Hashaamgtr/CAD_Project/review/06_CATIA_V5_2026_Final_Task/image18.png

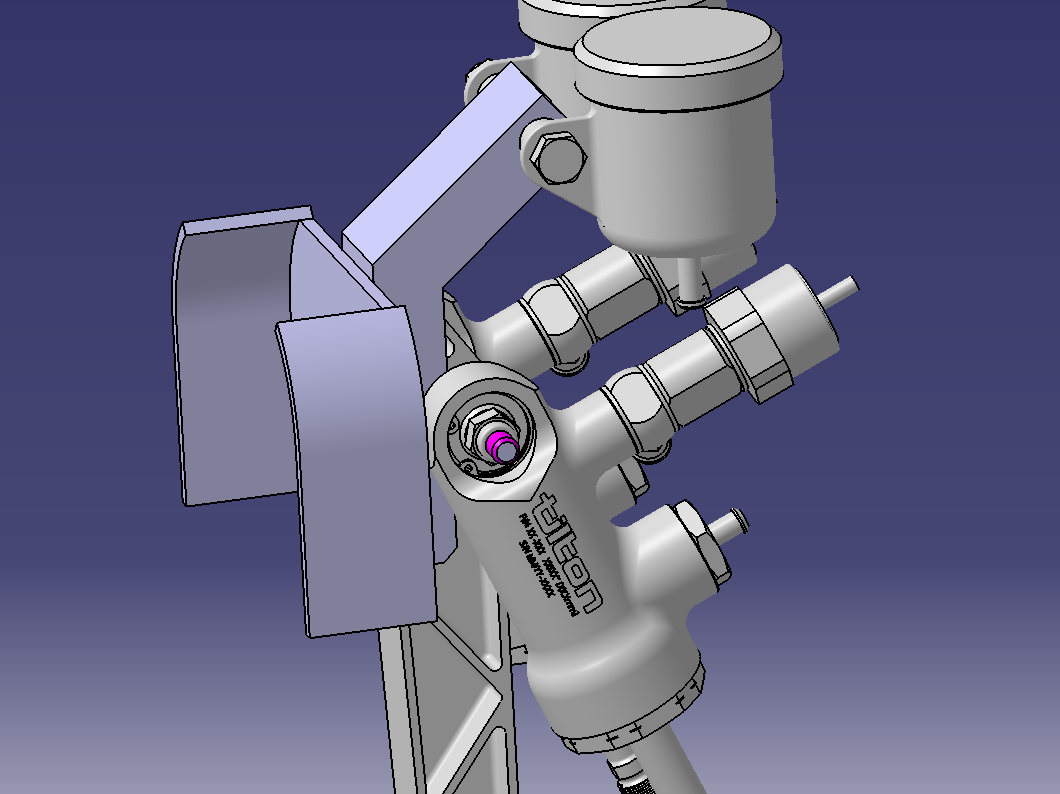
review/06_CATIA_V5_2026_Final_Task/image18.png
