Hashaamgtr/CAD_Project/review/06_CATIA_V5_2026_Final_Task/image20.png

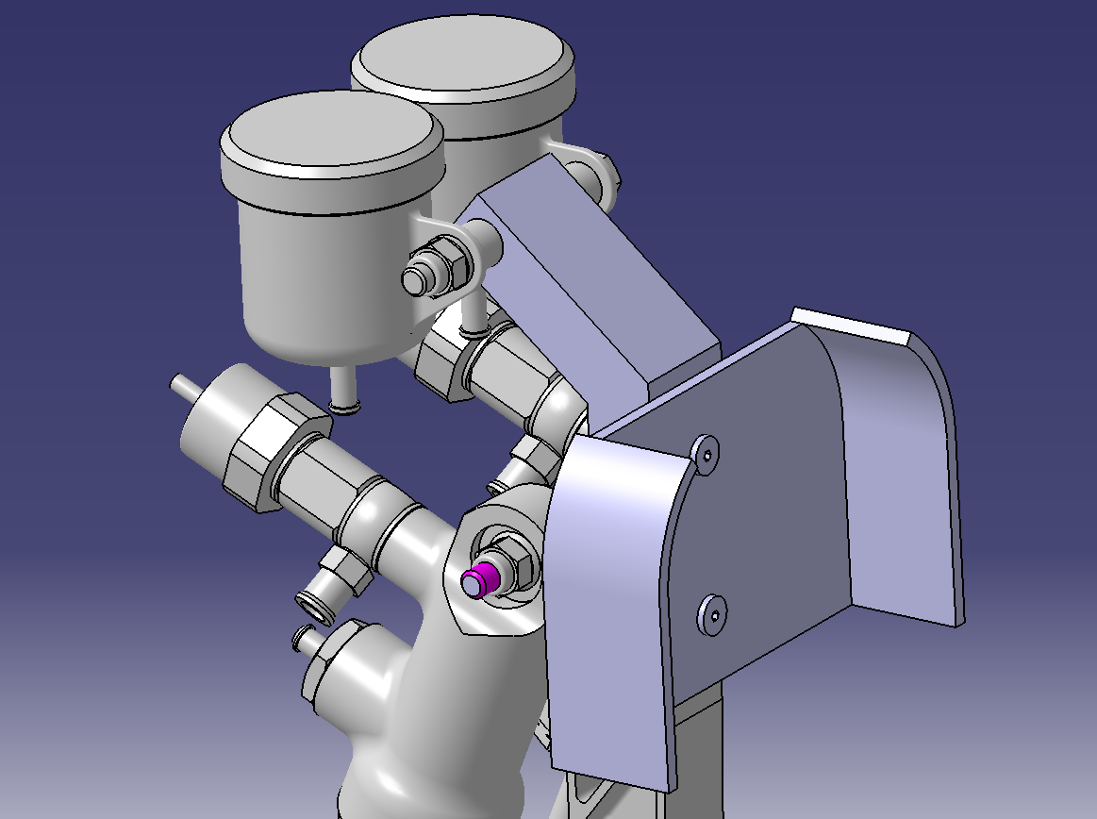
review/06_CATIA_V5_2026_Final_Task/image20.png
