Hashaamgtr/CAD_Project/review/Brake_Pedal_Shaft.bmp

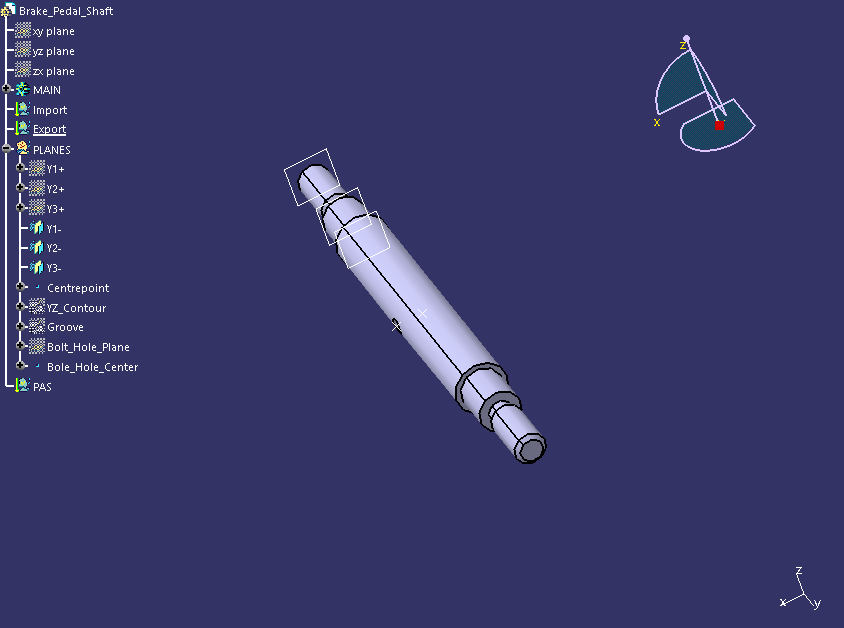
review/Brake_Pedal_Shaft.bmp
