Hashaamgtr/CAD_Project/review/Brake_Platform_2_positioned.bmp

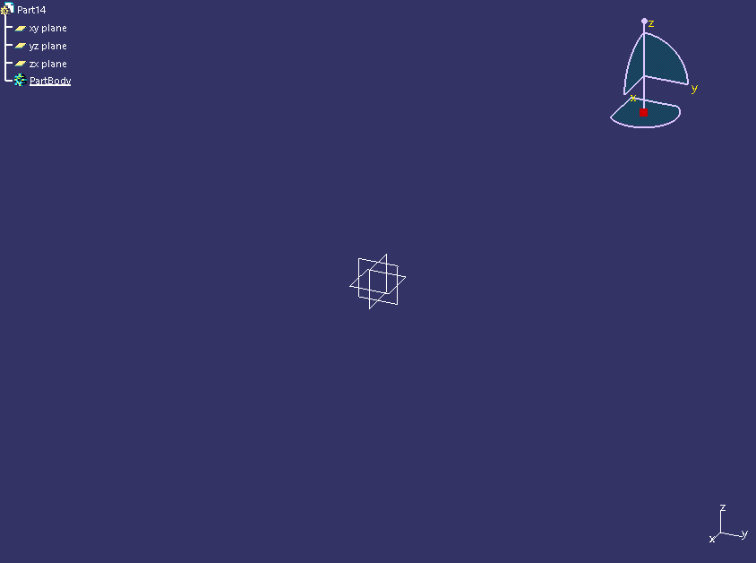
review/Brake_Platform_2_positioned.bmp
