Hashaamgtr/CAD_Project/review/BRK_PRS_Sensor_Connection_live.bmp

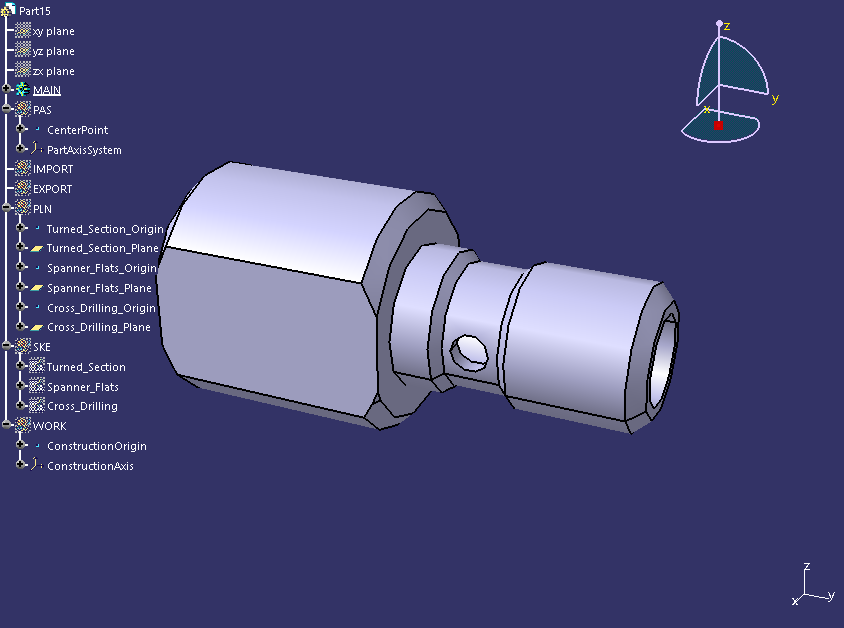
review/BRK_PRS_Sensor_Connection_live.bmp
