Hashaamgtr/CAD_Project/review/Foot_Plate.bmp

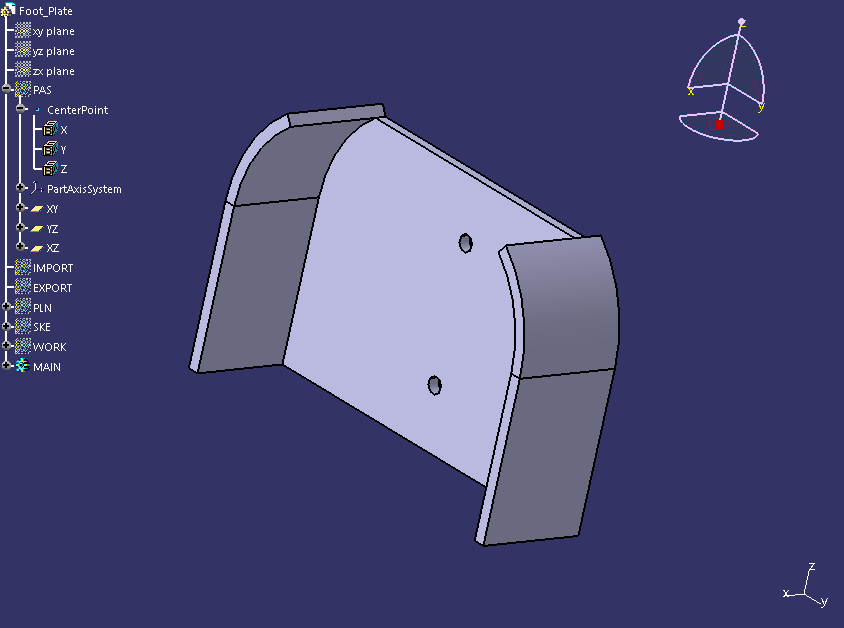
review/Foot_Plate.bmp
