Hashaamgtr/CAD_Project/review/MC_Inlet_live.bmp

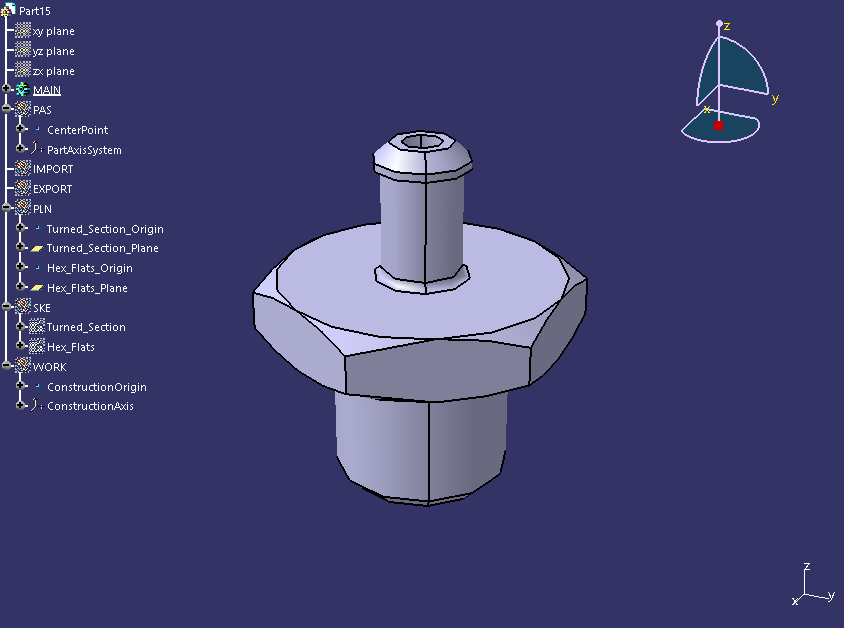
review/MC_Inlet_live.bmp
