Hashaamgtr/CAD_Project/review/Part1.bmp

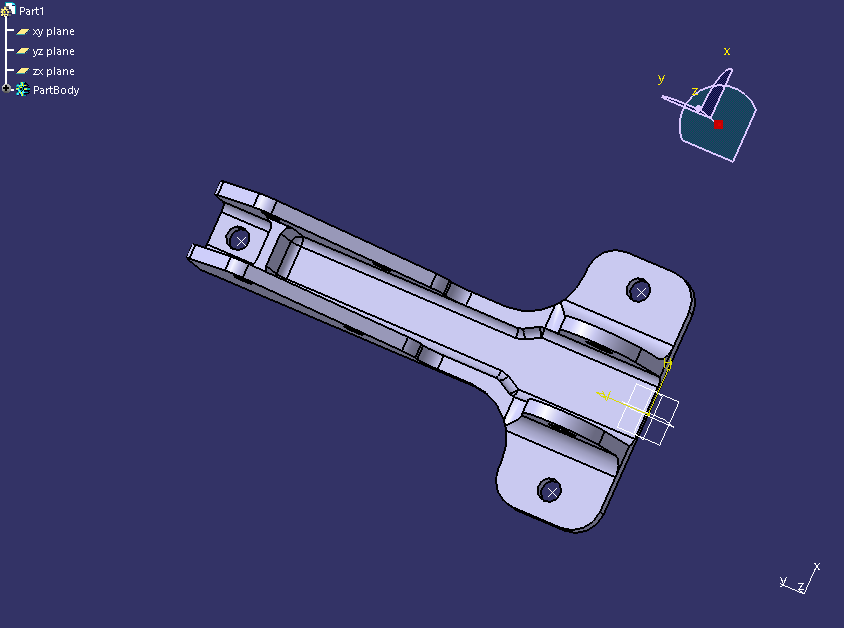
review/Part1.bmp
