Hashaamgtr/CAD_Project/review/Part 2&3.bmp

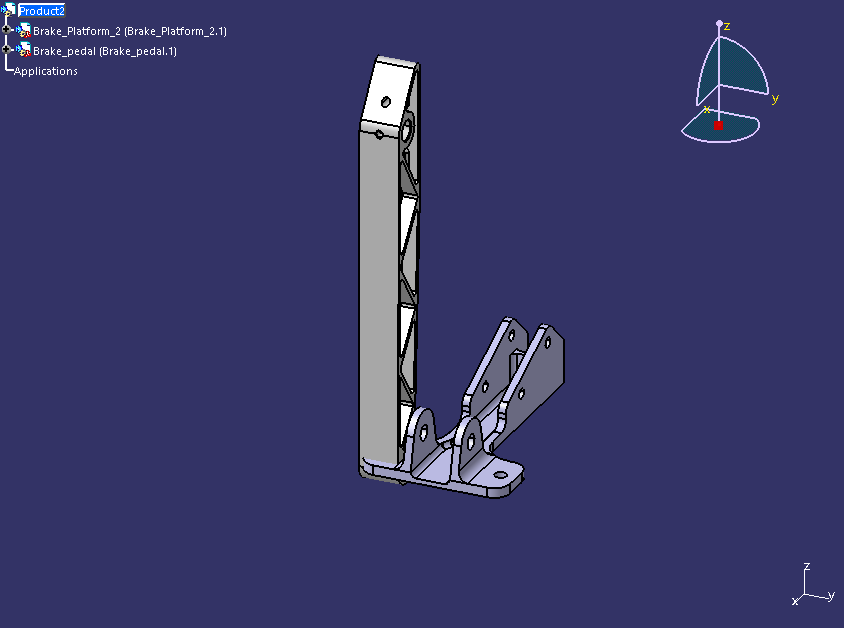
review/Part 2&3.bmp
