Hashaamgtr/CAD_Project/review/Part 2&3_actual.bmp

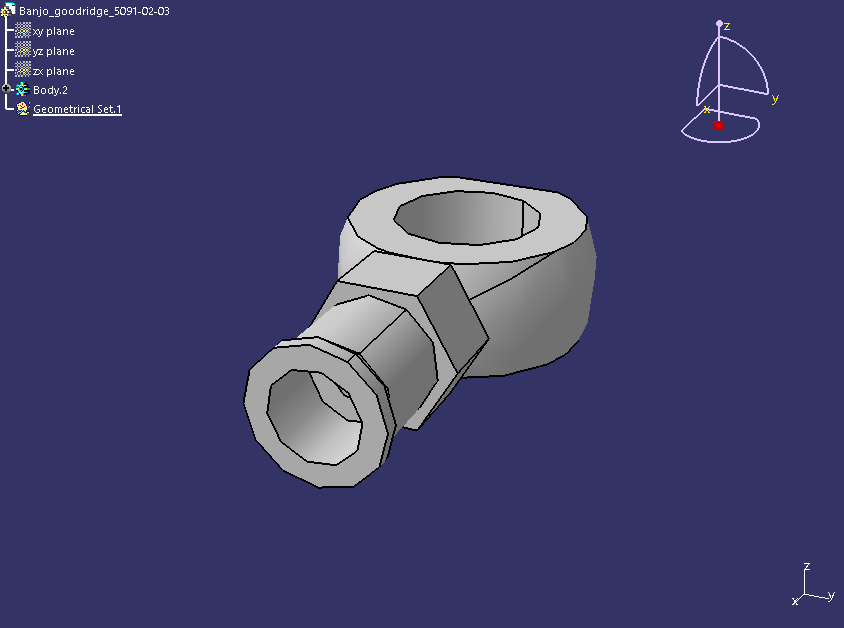
review/Part 2&3_actual.bmp
