Hashaamgtr/CAD_Project/review/Pedal_Body_live.bmp

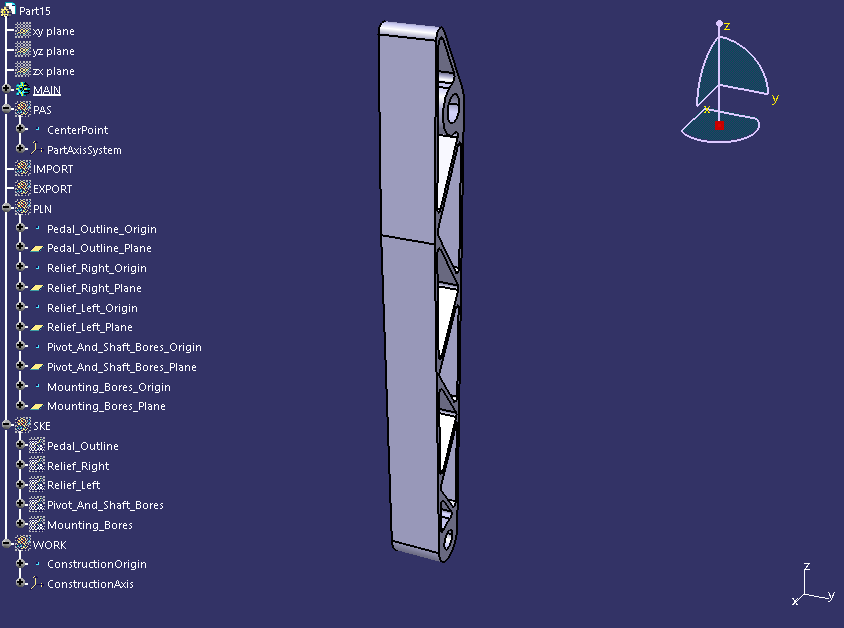
review/Pedal_Body_live.bmp
