Hashaamgtr/CAD_Project/review/Reservoir_Holder_positioned.bmp

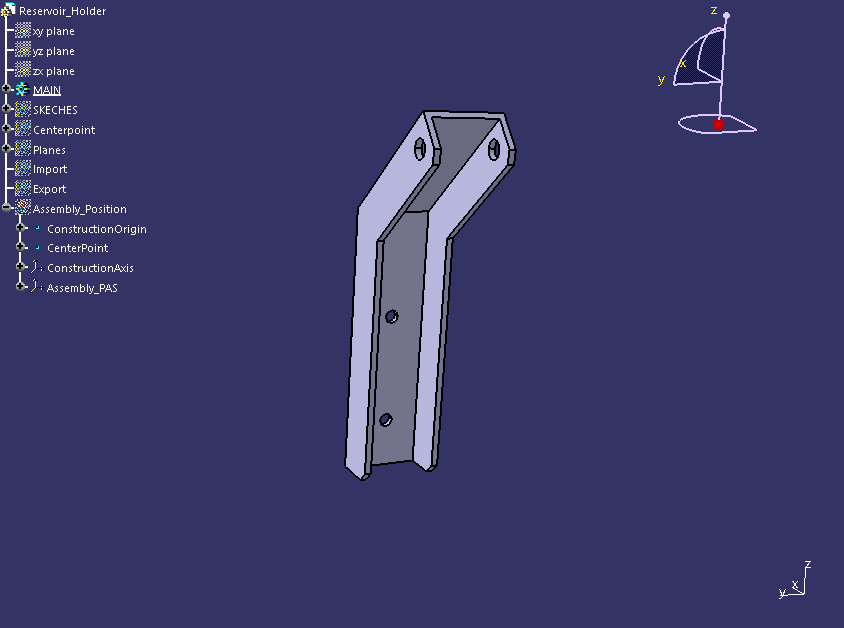
review/Reservoir_Holder_positioned.bmp
