Hashaamgtr/CAD_Project/reference_parts/Low_Head_M4x20.stp

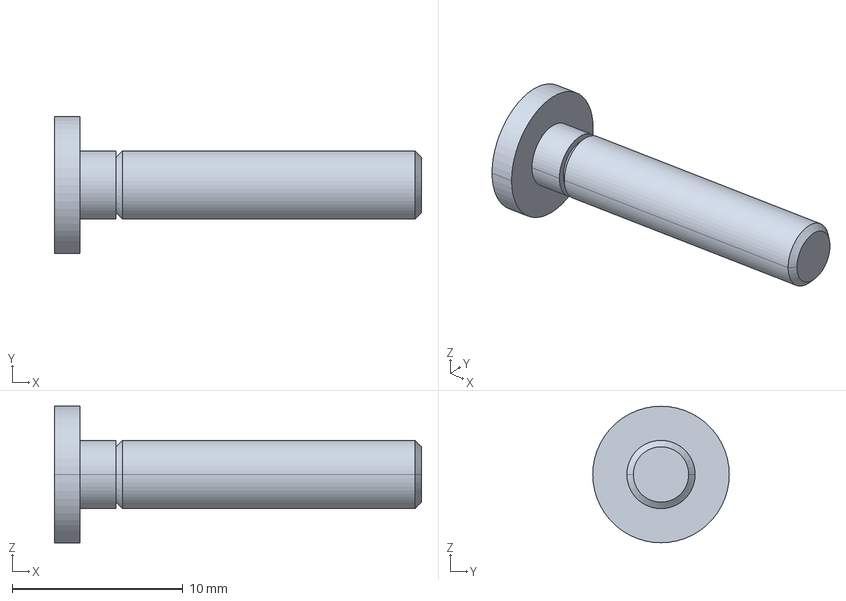
[picture p37: CAD file, 2026-10-06]
reference_parts/Low_Head_M4x20.stp
21.5 x 8.00 x 8.00 mm
