Hashaamgtr/CAD_Project/review/Brake_Platform_2_positioned.stp

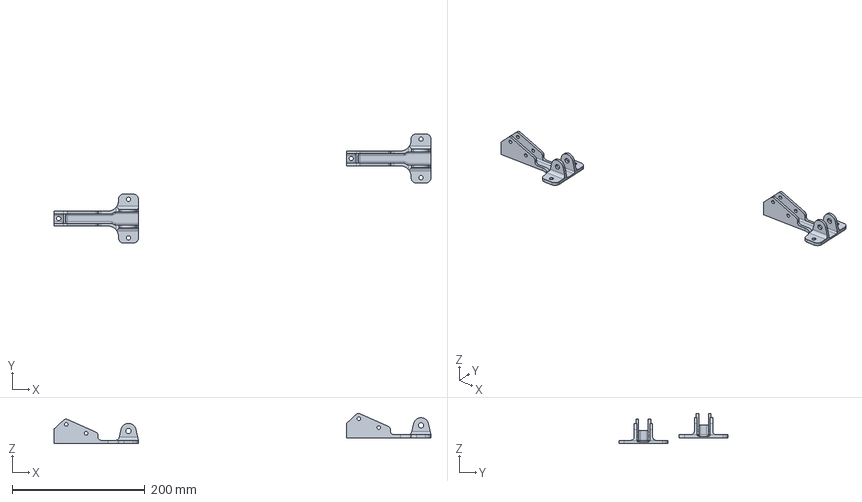
[picture p38: CAD file, 2026-10-06]
review/Brake_Platform_2_positioned.stp
567.0 x 164.5 x 45.4 mm
