Hashaamgtr/CAD_Project/reference_parts/Reservoir_Distance.stp

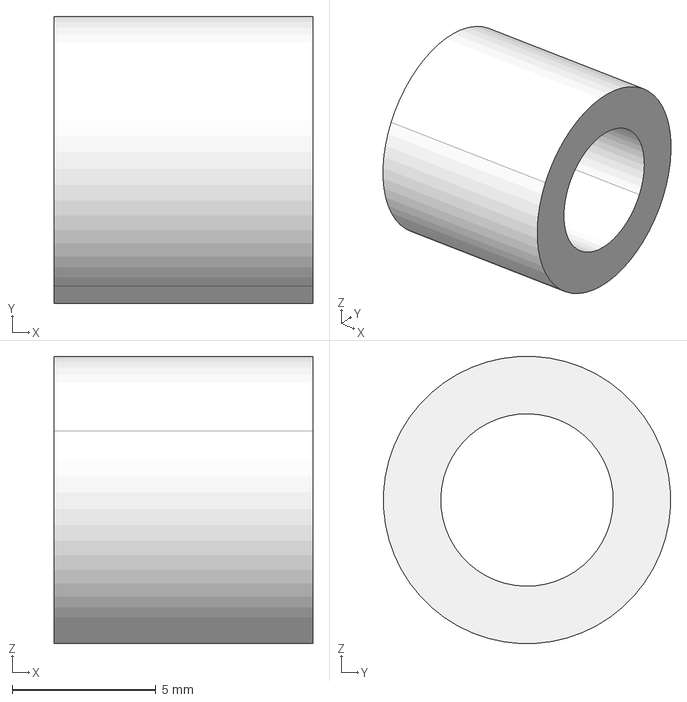
[picture p39: CAD file, 2026-10-06]
reference_parts/Reservoir_Distance.stp
9.00 x 9.99 x 9.99 mm
