Hashaamgtr/CAD_Project/reference_parts/BRK_PRS_Sensor.stp

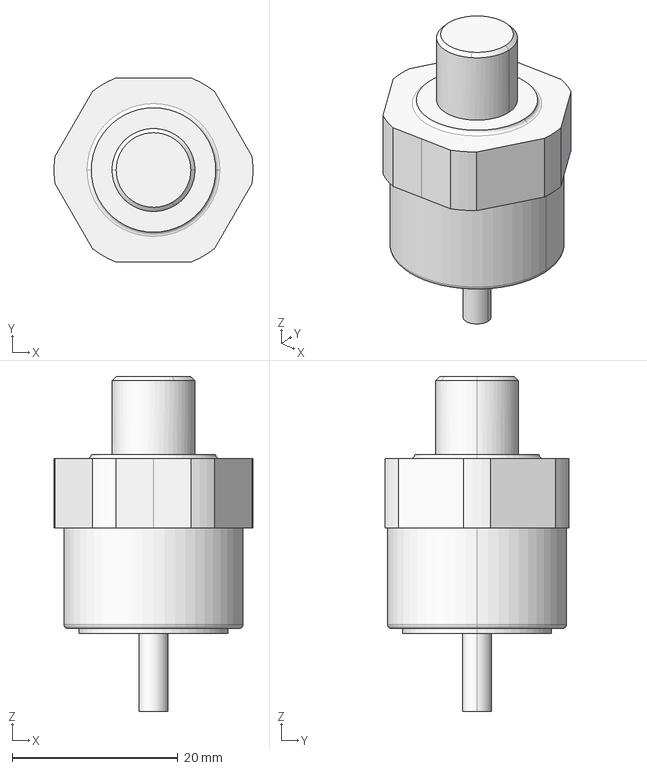
[picture p40: CAD file, 2026-10-06]
reference_parts/BRK_PRS_Sensor.stp
24.0 x 22.2 x 40.4 mm
