Hashaamgtr/CAD_Project/review/05_CATIA_V5_2026_ASSembly_Design/image16.png

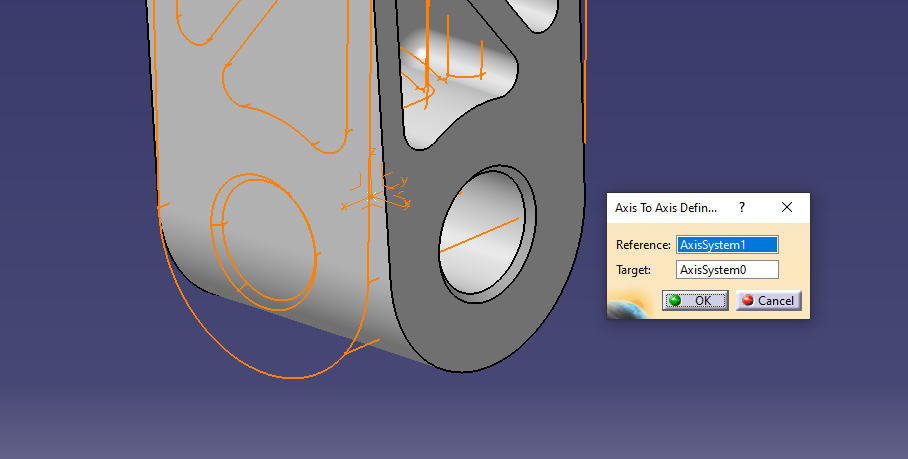
review/05_CATIA_V5_2026_ASSembly_Design/image16.png
